lsa-pucrs/rofi-biped-robot/resources/images/20140527_095114.jpg

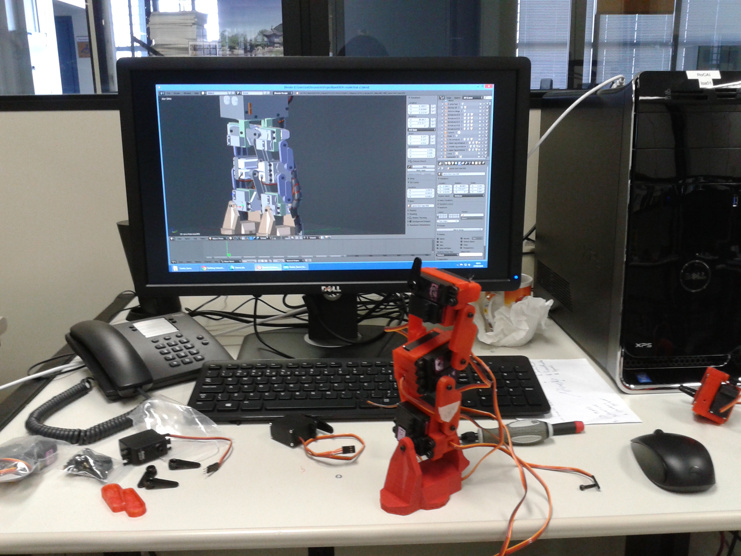
resources/images/20140527_095114.jpg
