lsa-pucrs/rofi-biped-robot/resources/images/20140527_095121.jpg

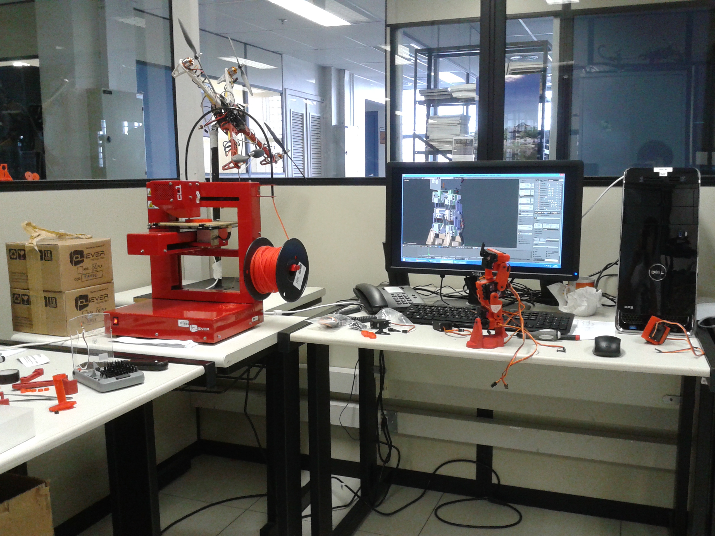
resources/images/20140527_095121.jpg
