lsa-pucrs/rofi-biped-robot/resources/images/20140529_145844.jpg

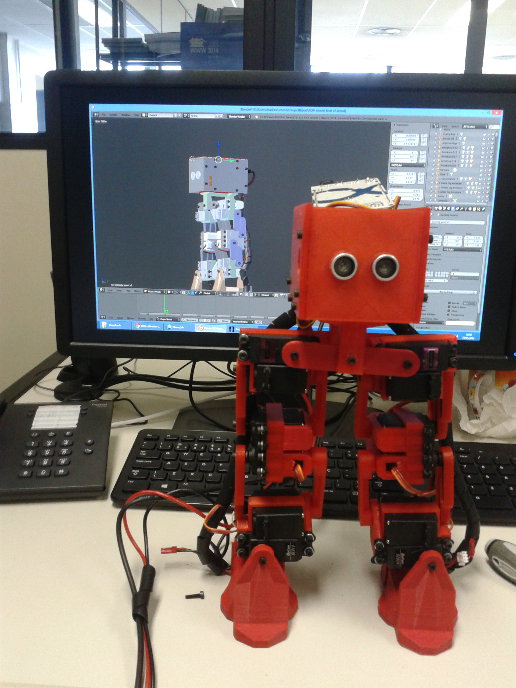
resources/images/20140529_145844.jpg
