lsa-pucrs/rofi-biped-robot/resources/images/20140613_101725.jpg

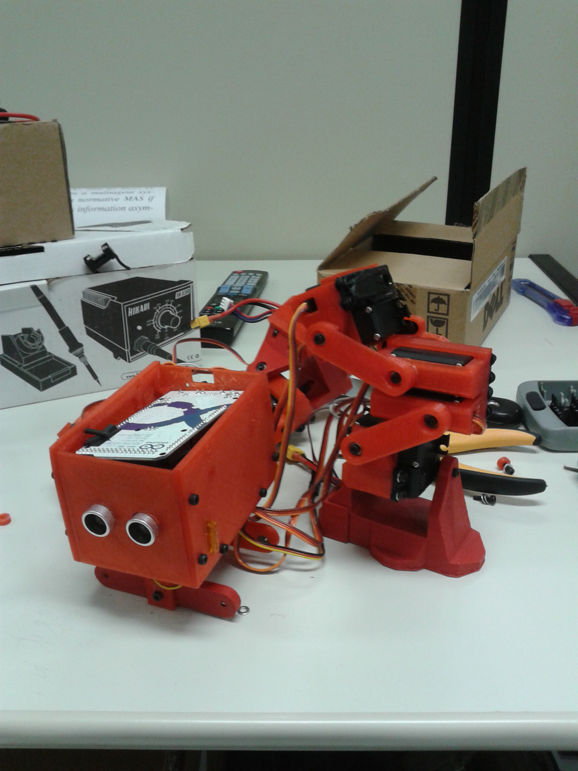
resources/images/20140613_101725.jpg
