lsa-pucrs/rofi-biped-robot/resources/images/20150212_114709.jpg

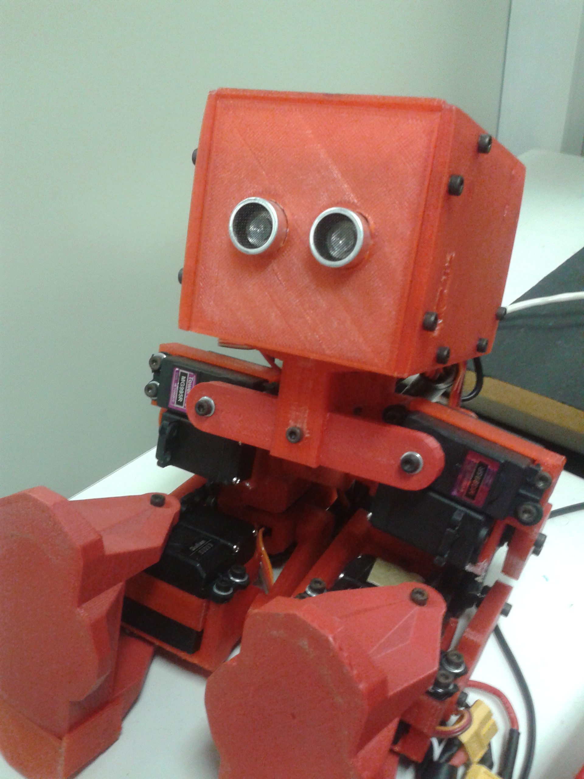
resources/images/20150212_114709.jpg
