lsa-pucrs/rofi-biped-robot/resources/images/20150212_114720.jpg

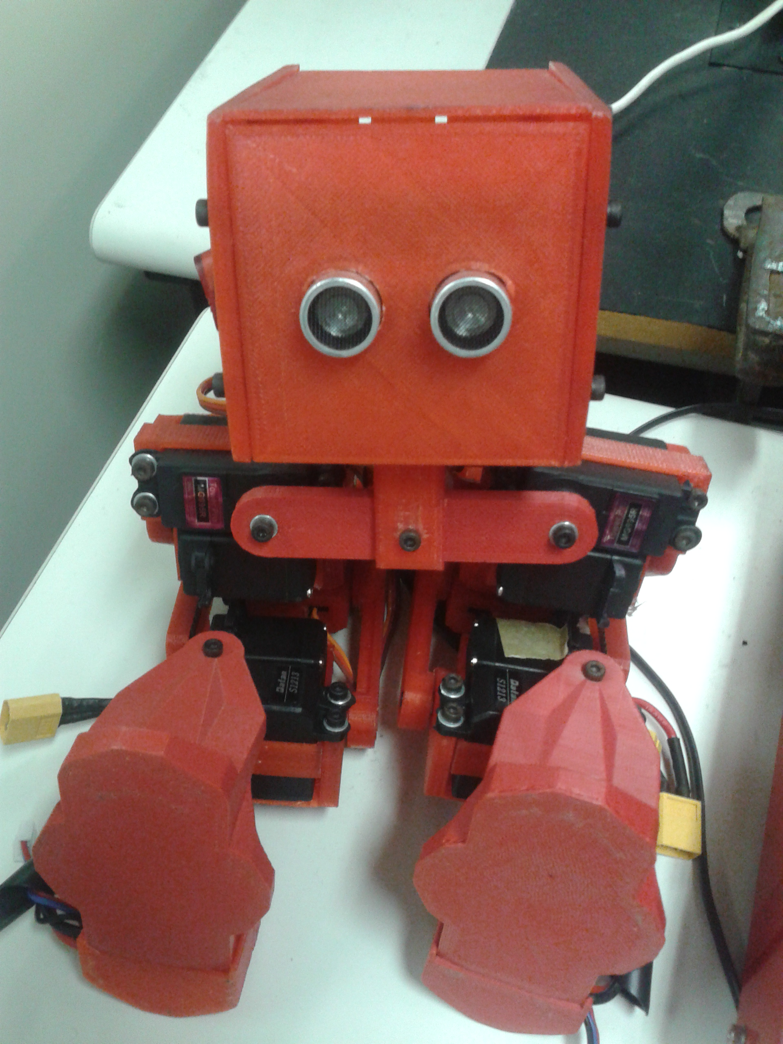
resources/images/20150212_114720.jpg
