lsa-pucrs/rofi-biped-robot/resources/images/20150212_114734.jpg

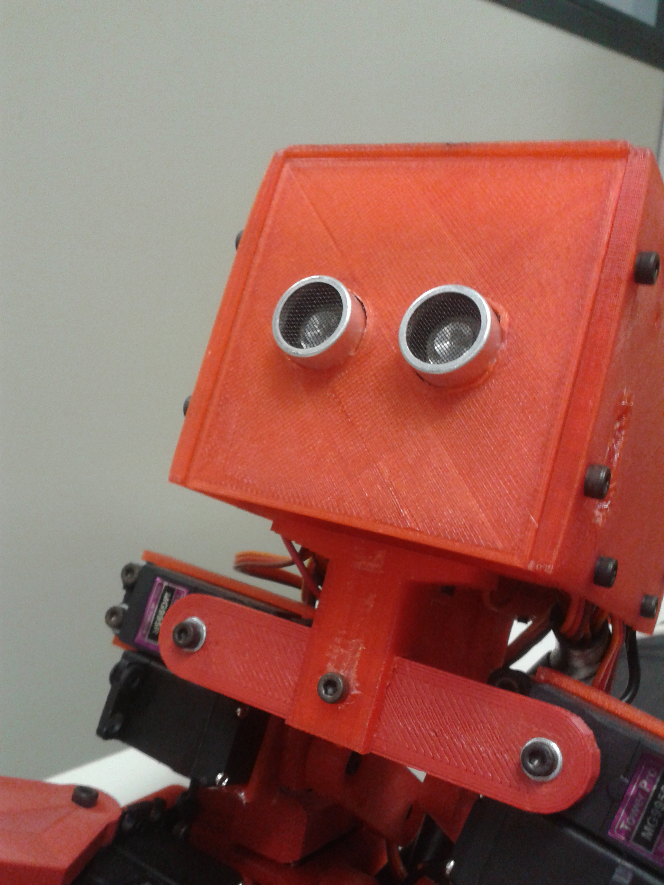
resources/images/20150212_114734.jpg
