lsa-pucrs/rofi-biped-robot/rofi_ros/scripts/rofi.py

import time
import copy
import math
import Adafruit_PCA9685

import numpy as np
import picamera as PC

from smbus2 import SMBus
from serial import Serial

import rospy
from std_msgs.msg import String

# =============================
# RIGHT LEG JOINTS
# 0 Right Ankle (roll)
# 1 Right Lower Leg
# 2 Right Knee
# 3 Right Middle Leg (trocado)
# 4 Right Upper Leg
# 5 Right Hip (roll)

# LEFT LEG JOINTS
# 6 Left Ankle (roll)
# 7 Left Lower Leg
# 8 Left Knee
# 9 Left Middle Leg
# 10 Left Upper Leg
# 11 Left Hip (roll)
# =============================

class action:
    def __init__(self, frames):
        self.numServos = 12
        self.numFrames = len(frames)
        self.frames = copy.deepcopy(frames)

        # can optimize perhaps
        # the calibration matrix is nothing more than the vector of the offsets of each servo
        new__calibration = [1300, 1100, 800, -7800, 1400, 300, 700, 3600, 1600, 300, 600, 1800]
        # the old calibration matrix is used to preserve the size of the interval between the offset and the maximum and minimum values
        # so we can use that to create new max and min values through the new offset
        old__calibration = [
            [8460 , -235 , -8865],
            [1785 , 83   ,  -943],
            [1600 , 421  ,  -578],
            [-1500, 1684 ,   724],
            [1900 , 124  , -1066],
            [0    , -861 , -1500],

            [9068 , 402  , -8800],
            [-700 , -1550, -1270],
            [1200 , 707  ,   -14],
            [-1500, 1656 ,  1021],
            [1900 , 1195 ,   740],
            [0    , -401 ,  -700]
        ]

        # this section does exactly what was described above
        self.calibration = [ [new__calibration[row] - (old__calibration[row][1] - old__calibration[row][0]), new__calibration[row], new__calibration[row] + (old__calibration[row][2] - old__calibration[row][1])] for row in range(len(old__calibration)) ]

        for f in range(len(frames)):            # for every frame
            for s in range(12):                 # for every servo
                if s >= 6:
                    self.frames[f][s] *= -1     # if servo is from the left side then invert the angle

        self.index = 0

        # calibrate in the initialization
        for f in range(self.numFrames):
            for s in range(self.numFrames):
                self.frames[f][s] = correctJointAngle(self.frames[f][s], s)

    def map(self, x, a, b, c, d):
        return (x - a) * (d - c) / (b - a) + c

    # Device is a Adafruit_PCA9685
    def setServoPos(self, device):
        for servo in range(self.numServos):
            device.set_pwm(servo, 0, int(self.map(self.getFrame()[servo], -4500, 4500, 204.8, 409.6)))

    # Correct the angles using a calibration matrix
    def correctJointAngle(angle, servo):
        if angle > 0:
            return self.map(angle, 0, 4500, 0 + self.calibration[servo][1], 4500 + self.calibration[servo][2])
        else:
            return self.map(angle, -4500, 0, -4500 + self.calibration[servo][0], 0 + self.calibration[servo][1])

    def getFrame(self):
        return self.frames[self.index]

    # Play the animation on the device
    def play(self, device):
        # for f in range(self.numFrames):
        #     for s in range(self.numServos):
        #         self.frames[f][s] = correctJointAngle(self.frames[f][s], s)

        while self.index < self.numFrames:
            self.setServoPos(device)
            self.index += 1
            time.sleep(20e-3)

        self.index = 0

class rofi:
    def __init__(self):
        self.name = "rofi"

        # Creates the adafruit device
        self.device = Adafruit_PCA9685.PCA9685()
        self.device.set_pwm_freq(50)

        # Creates the BUS interface
        self.bus = SMBus(1)

        # Sets the accelerometer address for the i2c
        self.accelerometer = 0x53

        self.bus.write_byte_data(self.accelerometer, 0x2D, 0x08)
        self.bus.write_byte_data(self.accelerometer, 0x31, 0x0B)
        self.bus.write_byte_data(self.accelerometer, 0x2C, 0x09)

        # Creates the serial communication
        self.serial = Serial('/dev/ttyACM0')

        # Declare actions for the animations
        # ================================== #

        self.STEP = action([
            [  707, -2393,     0,     0, -3100,  1800, -1800,     0,   800,     0,     0, -2300 ],
            [ 1990, -2130,     0,     0, -3100,  2664, -2578,     0,   800,     0,     0, -2300 ],
            [ 2497, -2234, -2771,  2867,  1248,  2847, -2604,     0,   800,     0,  -573, -1917 ],
            [ 2812, -2367, -5772,  5915,  5980,  2894, -2500,     0,   784,     0, -1190, -1507 ],
            [ 2618, -2109, -5499,  5068,  5789,  2839, -2500,     0,   634,     0, -1094, -1581 ],
            [ 2425, -1852, -5226,  4222,  5598,  2785, -2500,     0,   484,     0,  -999, -1655 ],
            [ 2232, -1594, -4953,  3376,  5407,  2730, -2500,     0,   334,     0,  -903, -1729 ],
            [ 2039, -1336, -4680,  2529,  5216,  2676, -2500,     0,   184,     0,  -808, -1803 ],
            [ 1845, -1078, -4407,  1683,  5025,  2621, -2500,     0,    34,     0,  -712, -1877 ],
            [ 1652,  -821, -4134,   836,  4834,  2566, -2500,     0,  -116,     0,  -617, -1951 ],
            [ 1459,  -563, -3861,    -9,  4642,  2512, -2500,     0,  -266,     0,  -521, -2026 ],
            [ 1370, -1976, -2600,     0,  1551,  2064, -2574,     0,  1400,     0, -4043, -1589 ],
            [ 1113,  -472, -2600,     0,  4383,  1381, -2074,     0,  1400,     0, -1100, -1396 ],
            [  462,  -482, -2620,     0,  4047,  1008, -1567,     0,  1416,     0, -1115, -1316 ],
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
            elif self.goal == 'forward':
                self.STEP.play(self.device)
            else:
                pass
        # ========================================= #

    def getDistance(self):
        return float(self.serial.readline())

    def getAcceleration(self):
        # calibration
        #       +9.8    -9.8
        # x -> 0x00F7, 0xFF07
        # y -> 0x00F8, 0xFEFB
        # z -> 0x00F7, 0xFF08

        # extra functions =================================== #
        def comp(x):
            return (x^0xFFFF) + 1

        def _map(x, a, b, c, d):
            return (x - a) * (d - c) / (b - a) + c
        # =================================================== #

        acc = [0, 0, 0]

        x0 = self.bus.read_byte_data(self.accelerometer, 0x32)
        x1 = self.bus.read_byte_data(self.accelerometer, 0x33)

        acc[0] = (x1 << 8) + x0

        y0 = self.bus.read_byte_data(self.accelerometer, 0x34)
        y1 = self.bus.read_byte_data(self.accelerometer, 0x35)

        acc[1] = (y1 << 8) + y0

        z0 = self.bus.read_byte_data(self.accelerometer, 0x36)
        z1 = self.bus.read_byte_data(self.accelerometer, 0x37)

        acc[2] = (z1 << 8) + y0

        cal = [(0x00F7, -0x00F9), (0x00F8, -0x0105), (0x00F7, -0x00F8)]

        for i in range(3):
            if acc[i] > 0xFFFF / 2 - 0.5:
                acc[i] = comp(acc[i]) * -1

            acc[i] = _map(acc[i], cal[i][1], cal[i][0], -9.8, 9.8)

        return acc


ROFI = rofi()

if __name__ == '__name__':
    rospy.init_node(ROFI.name, anonymous=False)
    rospy.Subscriber('/follower/goal', String, ROFI.run)
    rospy.spin()
